makserge/gps-logger/schematics/gps-logger.kicad_sch

## KiCad design schematics/gps-logger.kicad_sch (2026-09-24)

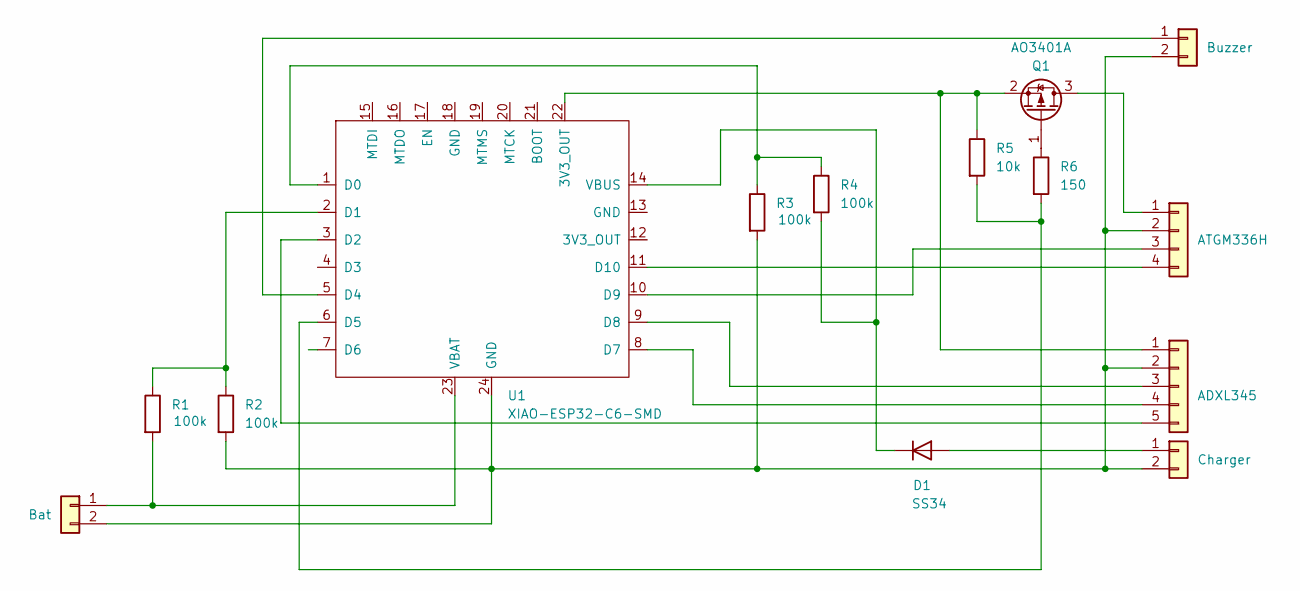
[picture p2: schematic gps-logger.kicad_sch]

Parts:
Buzzer1: Buzzer
D1: SS34; D_DO-35_SOD27_P7.62mm_Horizontal
J2: ADXL345
J6: ATGM336H
J7: Bat
J8: Charger
Q1: AO3401A; SOT-23
R1, R2, R3, R4: 100k
R5: 10k
R6: 150
U1: XIAO-ESP32-C6-SMD

Connections:
unnamed: Buzzer1.1, U1.5 (D4)
unnamed: Buzzer1.2, J2.2, J6.2, J7.2, J8.2, R2.2, R3.2, U1.24 (GND)
unnamed: D1.1 (K), R4.2, U1.14 (VBUS)
unnamed: D1.2 (A), J8.1
unnamed: J2.1, Q1.2 (S), R5.1, U1.22 (3V3_OUT)
unnamed: J2.3, U1.9 (D8)
unnamed: J2.4, U1.8 (D7)
unnamed: J2.5, U1.3 (D2)
unnamed: J6.1, Q1.3 (D)
unnamed: J6.3, U1.10 (D9)
unnamed: J6.4, U1.11 (D10)
unnamed: J7.1, R1.2, U1.23 (VBAT)
unnamed: Q1.1 (G), R6.1
unnamed: R1.1, R2.1, U1.2 (D1)
unnamed: R3.1, R4.1, U1.1 (D0)
unnamed: R5.2, R6.2, U1.6 (D5)
